AnthonyChen0921/SmartAC/Cedar_version_for_Gree/Cedar_version_for_Gree.ino

#include <IRremote.h>                  // 引用 IRRemote 函式库
#include <avr/pgmspace.h>
#include <avr/wdt.h>             // flash数据存储
#include <VoiceRecognition.h>    // 语音识别函数库
VoiceRecognition Voice;

// DATA BASE Infra
//Cold:
const PROGMEM unsigned int rawCodes_ac_16c[139] = {8916,4440,676,1604,680,516,676,516,676,1604,676,1604,676,1604,676,516,676,520,676,516,676,516,656,536,676,516,676,516,676,516,672,520,676,516,676,516,680,512,676,520,676,512,680,516,652,1628,676,516,676,1604,676,1604,660,532,676,516,676,520,652,1624,680,516,652,1628,676,516,676,516,676,1604,676,520,676,19812,696,516,676,520,676,516,676,516,676,1608,676,516,652,544,676,516,676,520,672,1608,676,516,676,520,676,516,652,1628,676,520,676,516,676,520,676,516,676,516,676,516,676,520,676,516,676,520,676,516,676,520,676,516,676,520,676,516,676,1604,676,1608,676,1604,676,520,676,
};  // 16c code
const PROGMEM unsigned int rawCodes_ac_17c[139] = {8916,4440,676,1604,676,516,676,516,676,1604,676,1604,680,1600,676,516,676,516,680,1604,676,512,680,516,676,516,676,516,676,516,676,516,676,516,676,516,680,516,676,516,676,516,676,512,676,1604,680,516,676,1604,676,1604,680,516,676,516,676,516,680,1600,680,512,676,1604,680,516,676,516,676,1604,676,516,680,19812,696,516,680,516,676,516,676,516,676,1604,676,520,676,516,676,520,676,516,676,1604,676,520,676,516,676,516,676,1604,680,512,680,516,676,516,676,516,676,520,676,516,676,516,676,516,676,516,676,520,676,516,676,516,680,516,676,516,676,516,680,512,680,516,676,1604,680,
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
};  // cold mode code
const PROGMEM unsigned int rawCodes_ac_warm[139] = {8936, 4428, 700, 500, 700, 500, 700, 1592, 676, 1616, 700, 1592, 676, 1592, 724, 1592, 700, 500, 676, 1616, 700, 1588, 680, 1620, 700, 496, 700, 500, 676, 520, 676, 488, 736, 500, 696, 500, 700, 500, 676, 480, 716, 524, 676, 524, 676, 1616, 696, 500, 676, 524, 676, 1616, 700, 500, 672, 524, 676, 524, 700, 1592, 676, 520, 704, 1592, 676, 520, 676, 524, 676, 1616, 676, 524, 700, 19852, 704, 1592, 676, 520, 676, 524, 700, 496, 676, 524, 676, 524, 700, 496, 676, 524, 700, 496, 676, 524, 676, 524, 700, 496, 704, 496, 676, 1616, 676, 500, 724, 496, 676, 524, 676, 520, 700, 500, 676, 524, 676, 520, 700, 500, 676, 520, 704, 496, 676, 524, 700, 496, 700, 500, 676, 524, 700, 496, 676, 524, 676, 520, 700, 500, 676
};  // warm mode code


int n;
int k;

int count = 0;
int count_close = 0;
int time_p = 0;

int buttonstate_op = 8; // open button
int buttonstate_on = 6;

int val_op = 0;  // Check state
int val_on = 0;  // Check state
int old_val_on = 0;
int state = 0;

int val = 0;            //存储获取到的PIR数值
int PIR_sensor = A0;    //指定PIR模拟端口 A0

#include <dht11.h>        // load temp and moisture detector
dht11 DHT11;
#define DHT11PIN 7
void(* resetFunc) (void) = 0; //制造重启命令

IRsend irsend;                          // 定义 IRsend 物件来发射红外线讯号


void setup()
{
  pinMode(PIR_sensor, INPUT);   //设置PIR模拟端口为输入模式
  pinMode(buttonstate_op, INPUT);
  pinMode(buttonstate_on, OUTPUT);

  pinMode(3, OUTPUT);

  Serial.begin(9600);    // 温度传感


}



void loop()
{

  while (1)
  {

  //  if (val_op == LOW)
  //  {
      digitalWrite(8, HIGH);
      



      val = analogRead(PIR_sensor);                        //DHT11温控模块，获取温湿度
      Serial.println();
      int chk = DHT11.read(DHT11PIN);
      Serial.print("Read sensor: ");
      Serial.print("Humidity (%): ");
      Serial.println((float)DHT11.humidity, 2);
      Serial.print("Temperature (oC): ");
      Serial.println((float)DHT11.temperature, 2);
      delay(2000);

      digitalWrite(8, LOW);


      if (val > 300)      // 人体红外传感数值  有人一般为600+ 没人则为0
      {
        Serial.print("count =");  // count值测试，决定温度区间
        Serial.print((int)count);
        count_close = 0;  // 红外感应关机条件，在有人的时候清零
        time_p = 0;       // 红外感应关机条件，计数器模块，可调节，在val值变化时清零

        if ((float)DHT11.temperature >= 24.0 and count == 0)
        {
          unsigned int shuzu_cl[139];
          for (k = 0; k < 139; k++)
          {
            shuzu_cl[k] = pgm_read_word_near(rawCodes_ac_cl + k);
          }
          irsend.sendRaw(shuzu_cl, 139, 38);
          Serial.println("cl code sended");
          count = 5;         //count变为5，不再满足=0条件，使16度代码只发送一次
          //测试count值
          Serial.print("count =");
          Serial.print((int)count);
          delay(10000);
        }


        if ((float)DHT11.temperature <= 20.0 and count == 0)
        {
          unsigned int shuzu_26w[139];
          for (k = 0; k < 139; k++)
          {
            shuzu_26w[k] = pgm_read_word_near(rawCodes_ac_26w + k);
          }
          irsend.sendRaw(shuzu_26w, 139, 38);
          Serial.println("26w code sended");
          count = 3;
          Serial.print("count =");
          Serial.print((int)count);
          delay(10000);
        }

        if (((float)DHT11.temperature > 20.0) and ((float)DHT11.temperature < 24.0))
        {
          count = 0;
          Serial.print("count =");
          Serial.print((int)count);
        }
      }
      else
      {

        if (count_close == 0 and time_p > 30) {
          unsigned int shuzu_cl[139];
          for (k = 0; k < 139; k++)
          {
            shuzu_cl[k] = pgm_read_word_near(rawCodes_ac_cl + k);
          }
          irsend.sendRaw(shuzu_cl, 139, 38);
          Serial.println("Close code sended");

          count_close = 5;
        }
        time_p = time_p + 1;
        delay(2000);
        Serial.print("time = ");
        Serial.print(time_p);
      }


  }
}
