AnthonyChen0921/SmartAC/Infra-Red_Receptor_Program/shoude.ino

/*
Copyright AnalysIR 2014
 
Please refer to the blog posting for conditions associated with use.
[url]http://www.analysir.com/blog/2014/03/19/air-conditioners-problems-recording-long-infrared-remote-control-signals-arduino/[/url]
 
Connections:
IR Receiver      Arduino
V+          ->  +5v
GND          ->  GND
Signal Out   ->  Digital Pin 2
(If using a 3V Arduino, you may connect V+ to +3V)
*/
 
#define LEDPIN 13
//you may increase this value on Arduinos with greater than 2k SRAM
#define maxLen 800
 
volatile  unsigned int irBuffer[maxLen]; //stores timings - volatile because changed by ISR
volatile unsigned int x = 0; //Pointer thru irBuffer - volatile because changed by ISR
 
void setup() {
  Serial.begin(9600); //change BAUD rate as required
  attachInterrupt(0, rxIR_Interrupt_Handler, CHANGE);//set up ISR for receiving IR signal
}
 
void loop() {
  // put your main code here, to run repeatedly:
 
  //Serial.println(F("Press the button on the remote now - once only"));
  delay(5000); // pause 5 secs
  if (x) { //if a signal is captured
    digitalWrite(LEDPIN, HIGH);//visual indicator that signal received
    Serial.println();
    Serial.print(F("Raw: (")); //dump raw header format - for library
    Serial.print((x - 1));
    Serial.print(F(") "));
    detachInterrupt(0);//stop interrupts & capture until finshed here
    for (int i = 1; i < x; i++) { //now dump the times
      //if (!(i & 0x1)) Serial.print(F("-"));
      Serial.print(irBuffer[i] - irBuffer[i - 1]);
      Serial.print(F(","));
    }
    x = 0;
    Serial.println();
    Serial.println();
    digitalWrite(LEDPIN, LOW);//end of visual indicator, for this time
    attachInterrupt(0, rxIR_Interrupt_Handler, CHANGE);//re-enable ISR for receiving IR signal
  }
 
}
 
void rxIR_Interrupt_Handler() {
  if (x > maxLen) return; //ignore if irBuffer is already full
  irBuffer[x++] = micros(); //just continually record the time-stamp of signal transitions
 
}
